MOSH-Insa-Toulouse/2023-2024-4GP_MANENT_ZUPPELLI/images_projet_capteur/circuits_electroniques.png

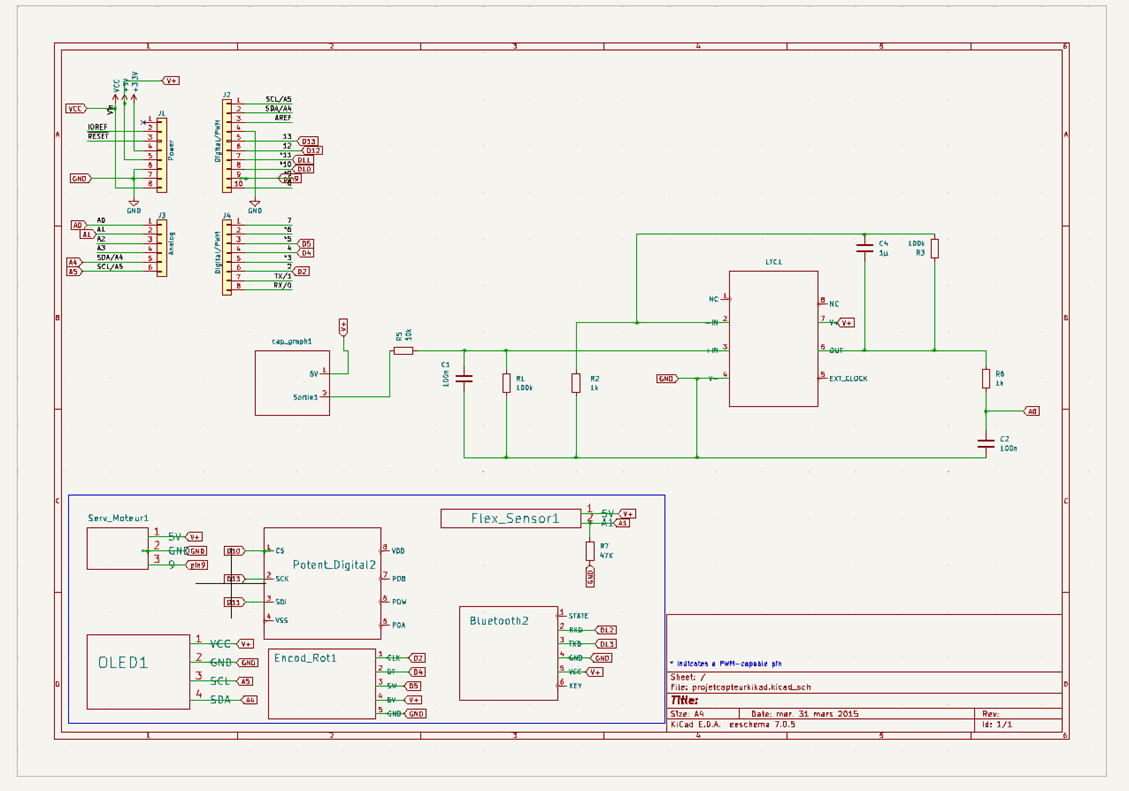
images_projet_capteur/circuits_electroniques.png
